ethz-pll/Blattdurchmesser/Catia/Saegeblatt_Schlitten.pdf

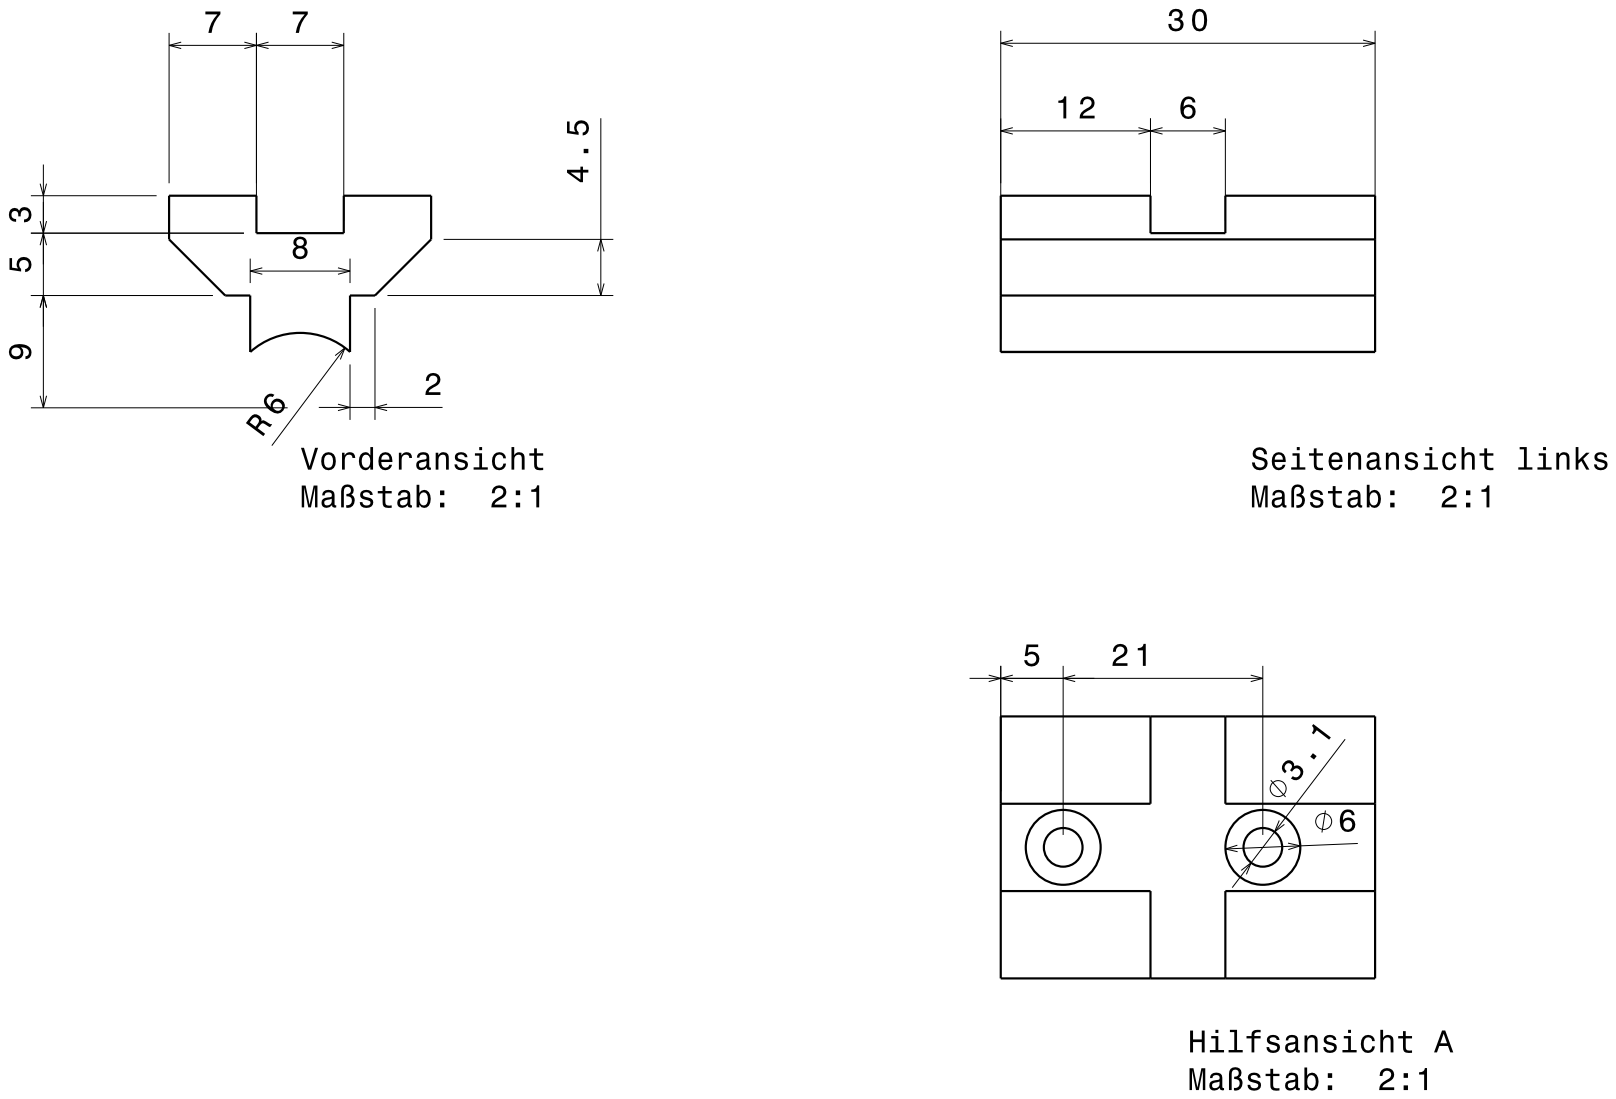
[picture p36: page 1]
